s54mtb/cabletester/img/pcb-bot.JPG

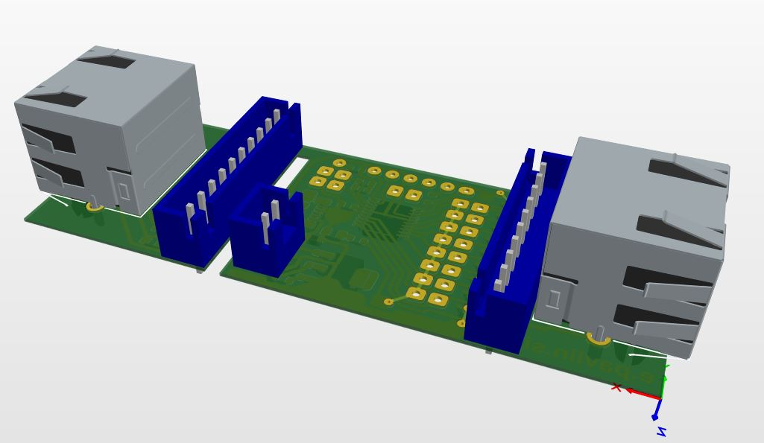
img/pcb-bot.JPG
