s54mtb/cabletester/img/remote.jpg

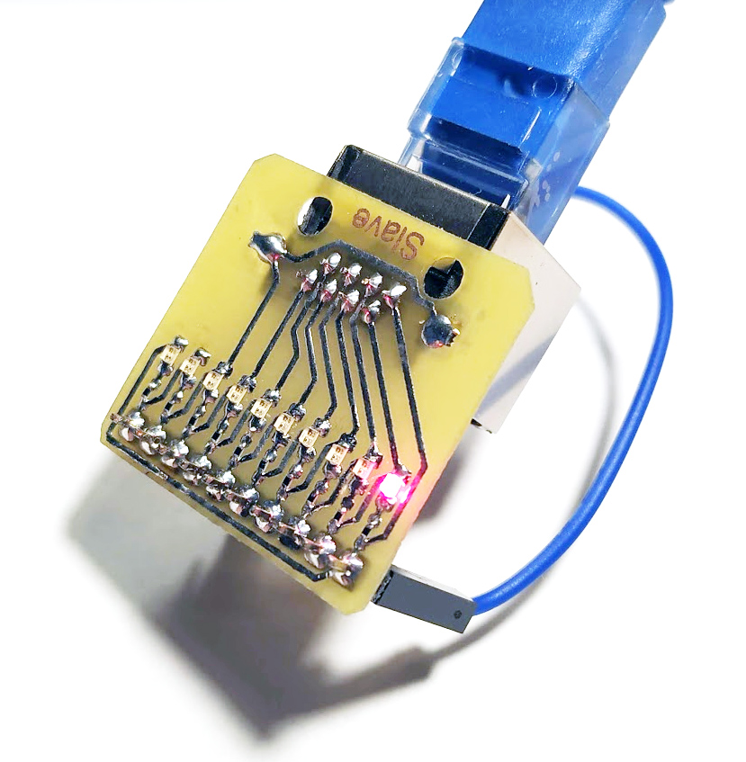
img/remote.jpg
